Filip-Lennhager/Precision-Lapping-Machine/Gearbox/Body1_5.stl

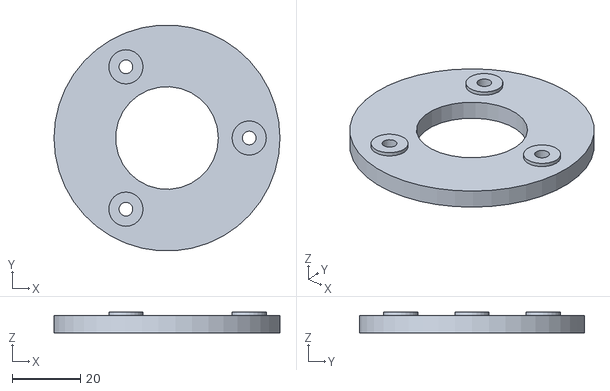
[picture p38: CAD file, 2023-05-24]
Gearbox/Body1_5.stl
66.0 x 65.8 x 6.00
