Filip-Lennhager/Precision-Lapping-Machine/Prototype/Disk and Bearing Housing/ballcaster.SLDPRT

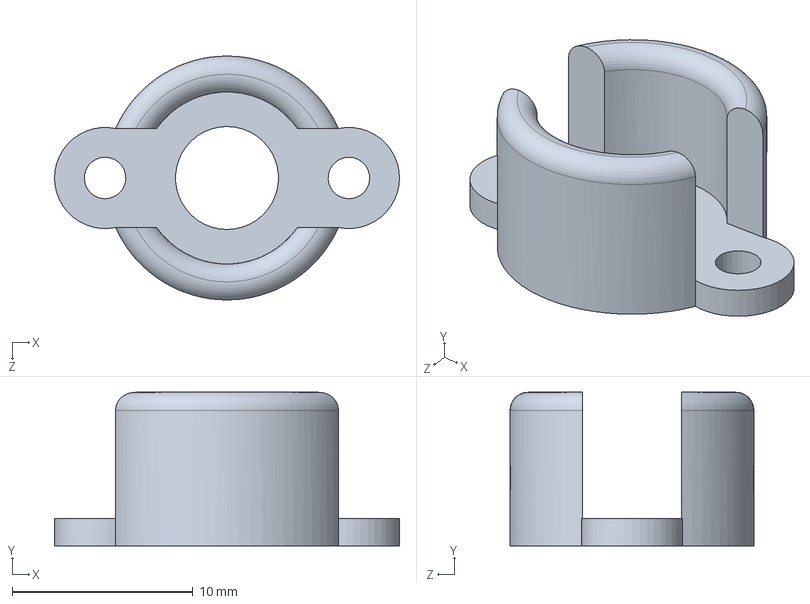
[picture p39: CAD file, 2023-05-24]
Prototype/Disk and Bearing Housing/ballcaster.SLDPRT
19.1 x 8.50 x 13.5 mm
