Filip-Lennhager/Precision-Lapping-Machine/Prototype/Weight/smallPiece.SLDPRT

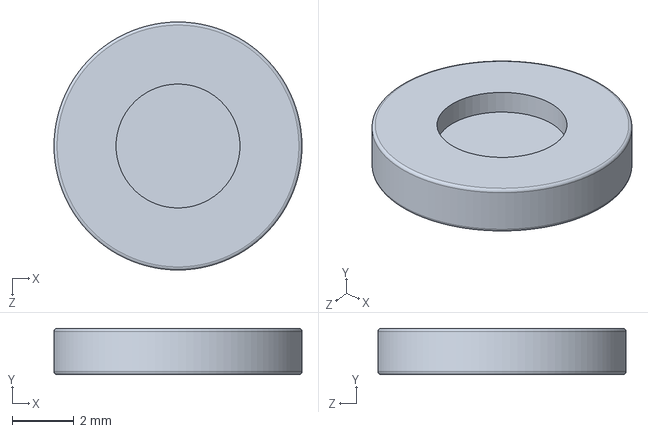
[picture p40: CAD file, 2023-05-24]
Prototype/Weight/smallPiece.SLDPRT
8.00 x 1.50 x 8.00 mm
