Filip-Lennhager/Precision-Lapping-Machine/Prototype/Disk and Bearing Housing/Stand.SLDPRT

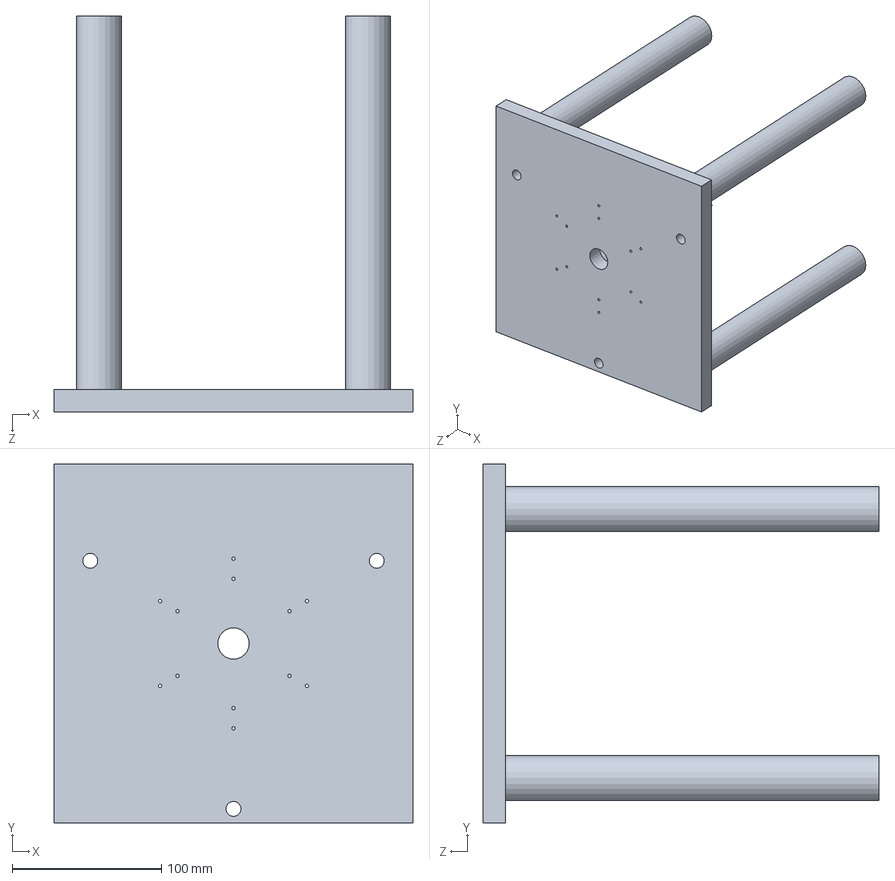
[picture p41: CAD file, 2023-05-24]
Prototype/Disk and Bearing Housing/Stand.SLDPRT
240.0 x 240.0 x 265.0 mm
