Filip-Lennhager/Precision-Lapping-Machine/Prototype/Weight/yogaMat.SLDPRT

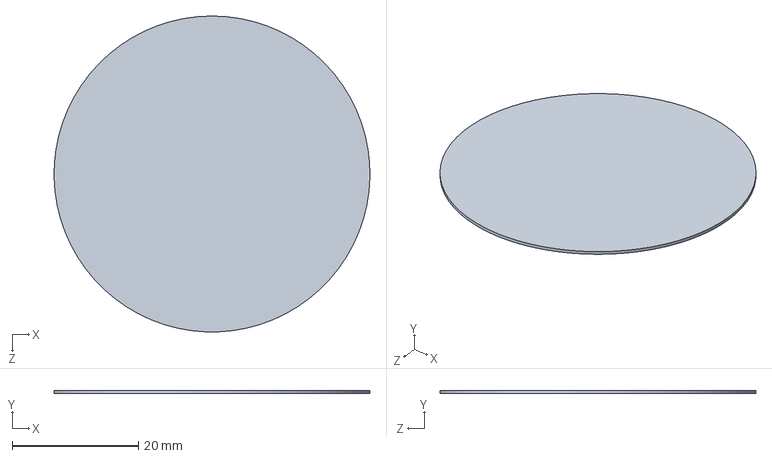
[picture p42: CAD file, 2023-05-24]
Prototype/Weight/yogaMat.SLDPRT
50.0 x 0.5 x 50.0 mm
