Filip-Lennhager/Precision-Lapping-Machine/Prototype/Disk and Bearing Housing/bearingArm.SLDPRT

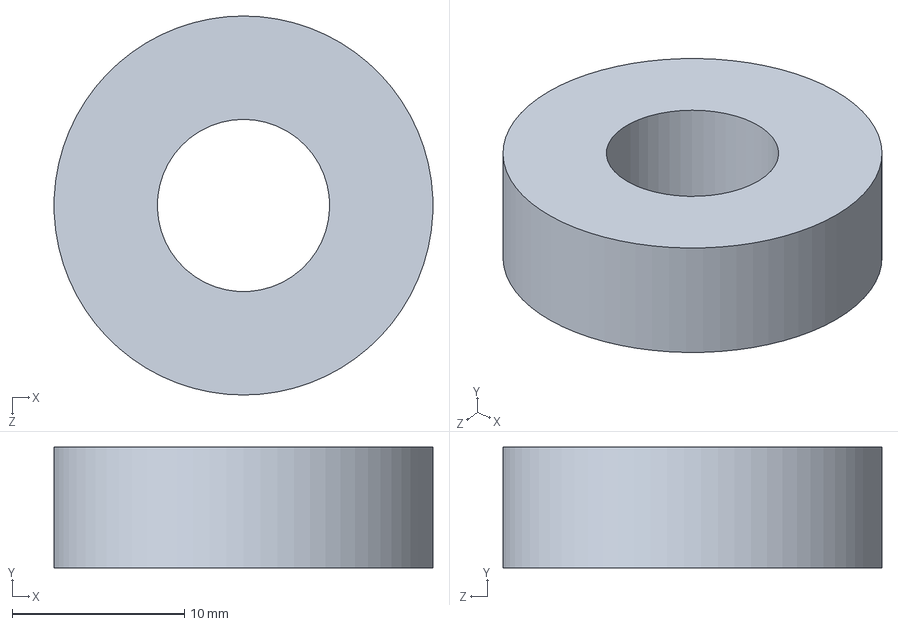
[picture p43: CAD file, 2023-05-24]
Prototype/Disk and Bearing Housing/bearingArm.SLDPRT
22.0 x 7.00 x 22.0 mm
