Filip-Lennhager/Precision-Lapping-Machine/Prototype/Weight/sandCyl.SLDPRT

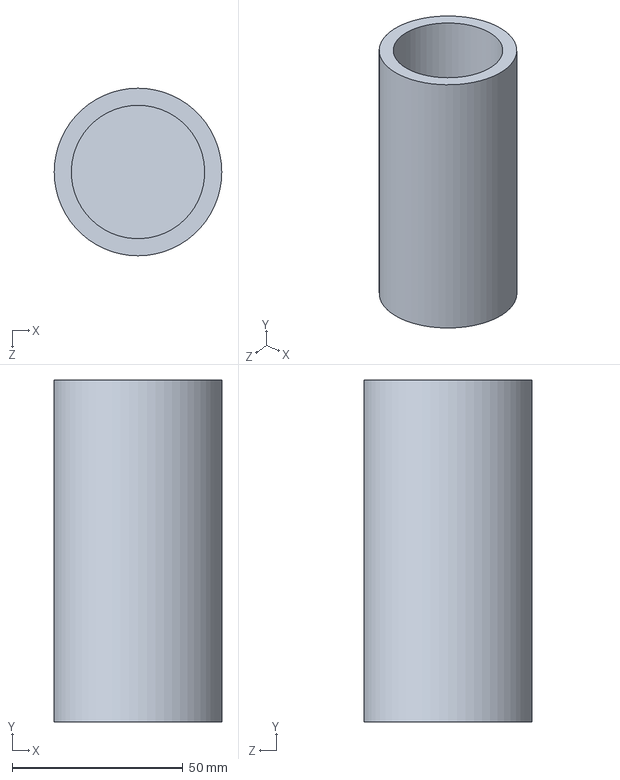
[picture p44: CAD file, 2023-05-24]
Prototype/Weight/sandCyl.SLDPRT
49.0 x 100.0 x 49.0 mm
