Filip-Lennhager/Precision-Lapping-Machine/Gearbox/Body1_7.stl

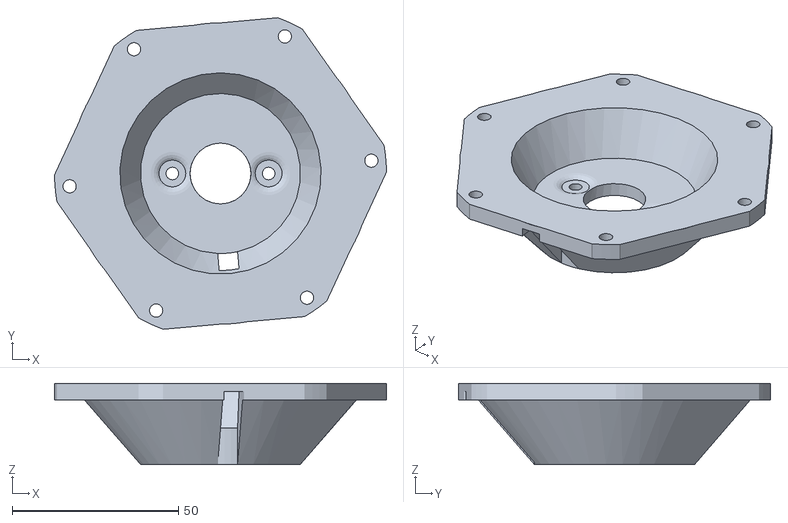
[picture p45: CAD file, 2023-05-24]
Gearbox/Body1_7.stl
100.0 x 93.8 x 24.5
