Filip-Lennhager/Precision-Lapping-Machine/Prototype/Disk and Bearing Housing/SpinningPart.SLDPRT

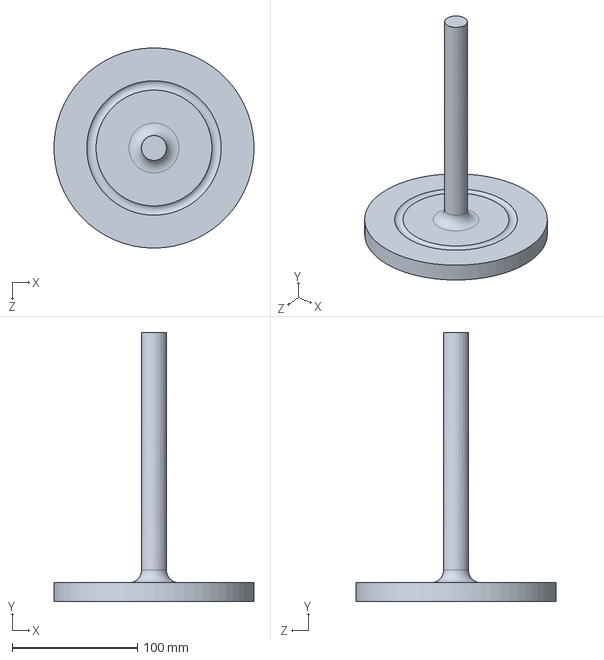
[picture p46: CAD file, 2023-05-24]
Prototype/Disk and Bearing Housing/SpinningPart.SLDPRT
159.8 x 215.0 x 160.0 mm
