Filip-Lennhager/Precision-Lapping-Machine/Prototype/Weight/hardBorderPart.SLDPRT

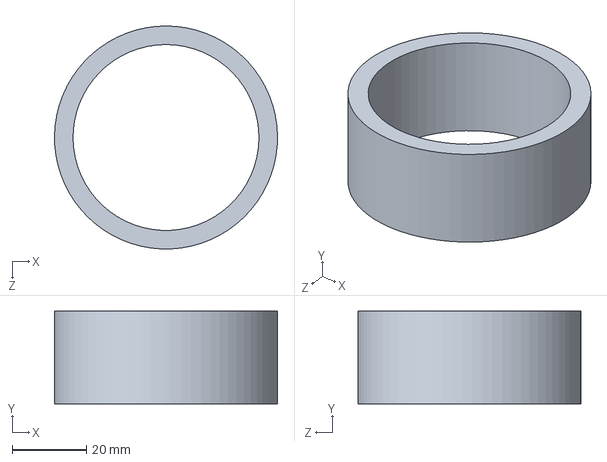
[picture p47: CAD file, 2023-05-24]
Prototype/Weight/hardBorderPart.SLDPRT
60.0 x 25.0 x 60.0 mm
