Filip-Lennhager/Precision-Lapping-Machine/Gearbox/Body1_8.stl

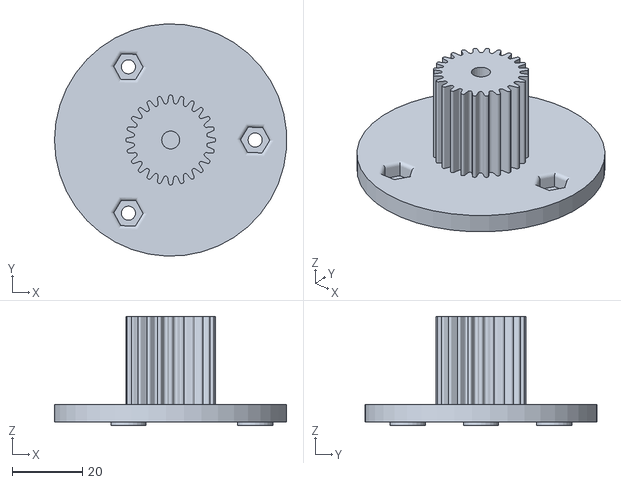
[picture p48: CAD file, 2023-05-24]
Gearbox/Body1_8.stl
65.9 x 66.0 x 31.0
