Filip-Lennhager/Precision-Lapping-Machine/Prototype/Weight/bigPiece.SLDPRT

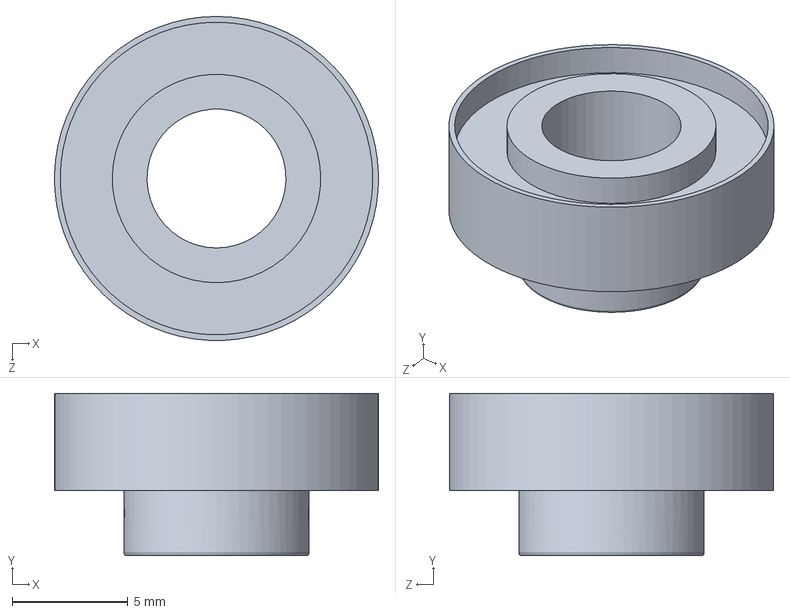
[picture p49: CAD file, 2023-05-24]
Prototype/Weight/bigPiece.SLDPRT
14.0 x 7.00 x 14.0 mm
