Filip-Lennhager/Precision-Lapping-Machine/Gearbox/Body13 modified.STL

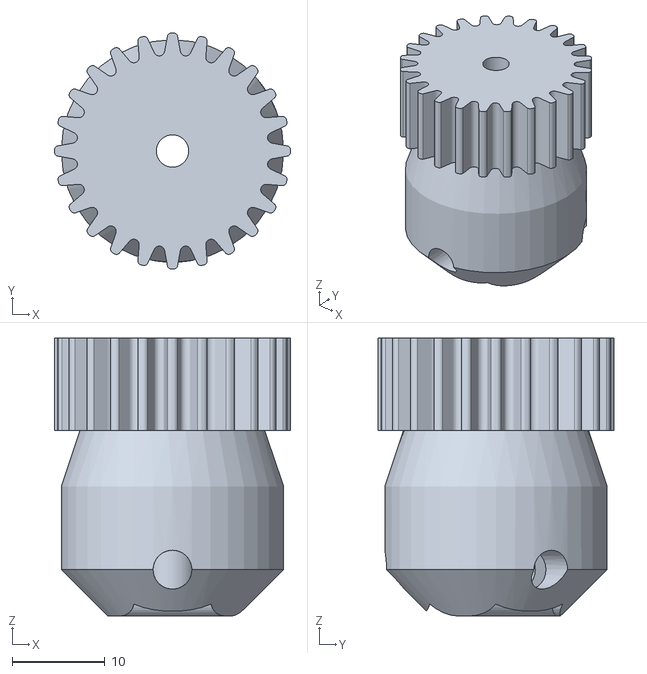
[picture p50: CAD file, 2023-05-24]
Gearbox/Body13 modified.STL
25.5 x 25.5 x 30.0
